justinkang221/das_pan/website/img/feature/pickup.gif

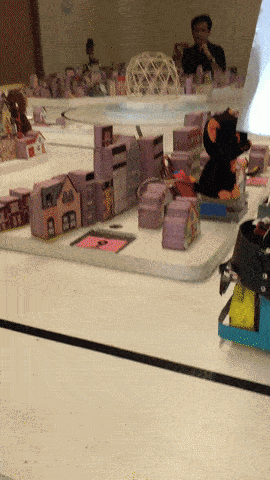
website/img/feature/pickup.gif
