justinkang221/das_pan/website/img/feature/pickup.jpg

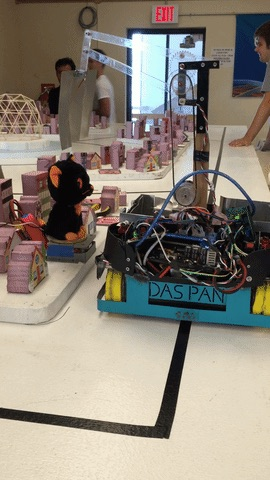
website/img/feature/pickup.jpg
