justinkang221/das_pan/website/img/texture/map.png

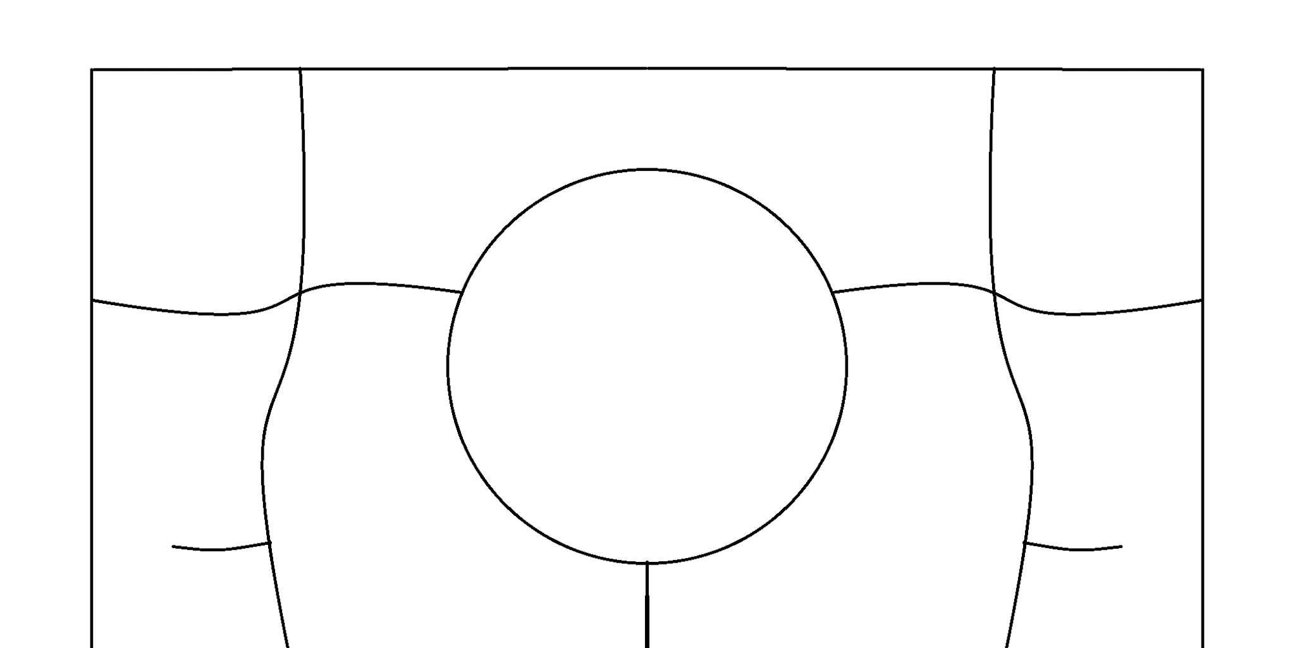
website/img/texture/map.png
